leech001/LeakControlESP8266/img/photo_2017-11-05_14-51-26.jpg

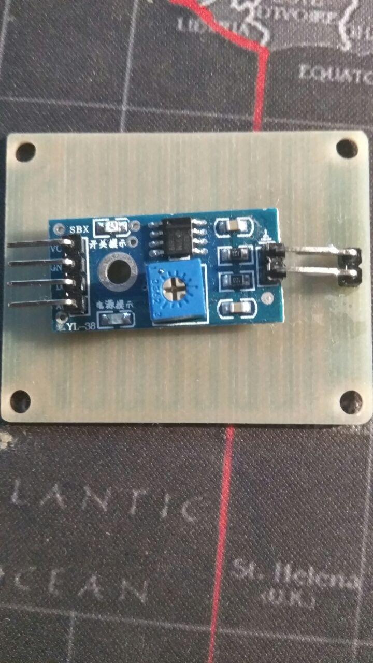
img/photo_2017-11-05_14-51-26.jpg
