leech001/LeakControlESP8266/src/esp8266/tap.py

from machine import Pin
import uasyncio as asyncio


class Tap:
    def __init__(self, pin_s, pin_d, tap_state):
        self.pin_s = pin_s
        self.pin_d = pin_d
        self.tap_state = tap_state

    async def open(self):
        Pin(self.pin_s, Pin.OUT, value=1)
        Pin(self.pin_d, Pin.OUT, value=1)
        await asyncio.sleep(10)
        Pin(self.pin_s, Pin.OUT, value=0)
        self.tap_state = "ready"
        return "Tap on pin %s is open" % self.pin_d

    async def close(self):
        Pin(self.pin_s, Pin.OUT, value=1)
        Pin(self.pin_d, Pin.OUT, value=0)
        await asyncio.sleep(10)
        Pin(self.pin_s, Pin.OUT, value=0)
        self.tap_state = "ready"
        return "Tap on pin %s is closed" % self.pin_d
